NeedfulThings/hyperionconfigs/UDP-ESP8266/assets/top_v1.1.png

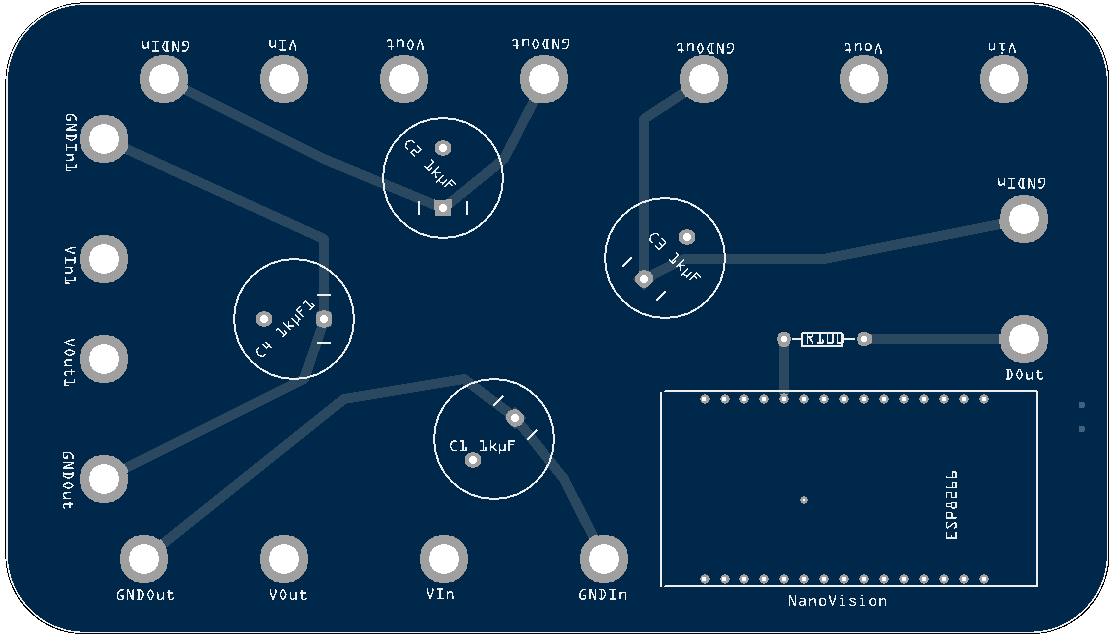
UDP-ESP8266/assets/top_v1.1.png
