NeedfulThings/hyperionconfigs/USB-UDP-Universal/layout/assets/back.png

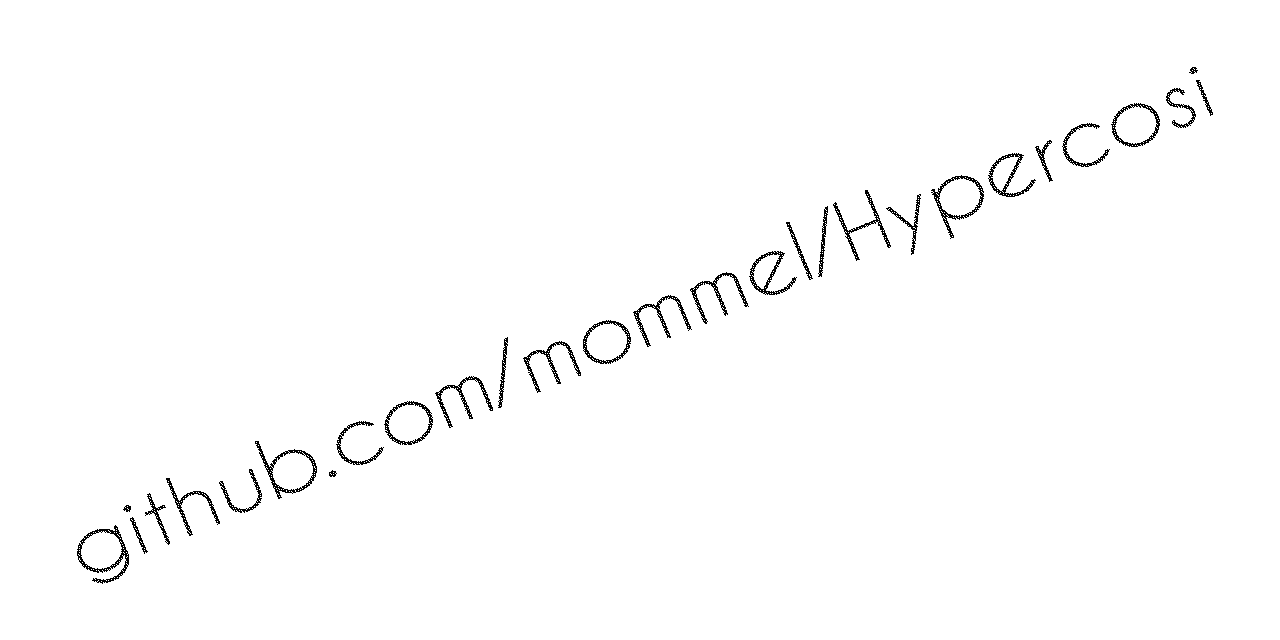
USB-UDP-Universal/layout/assets/back.png
