NeedfulThings/hyperionconfigs/USB-UDP-Universal/layout/assets/hw.png

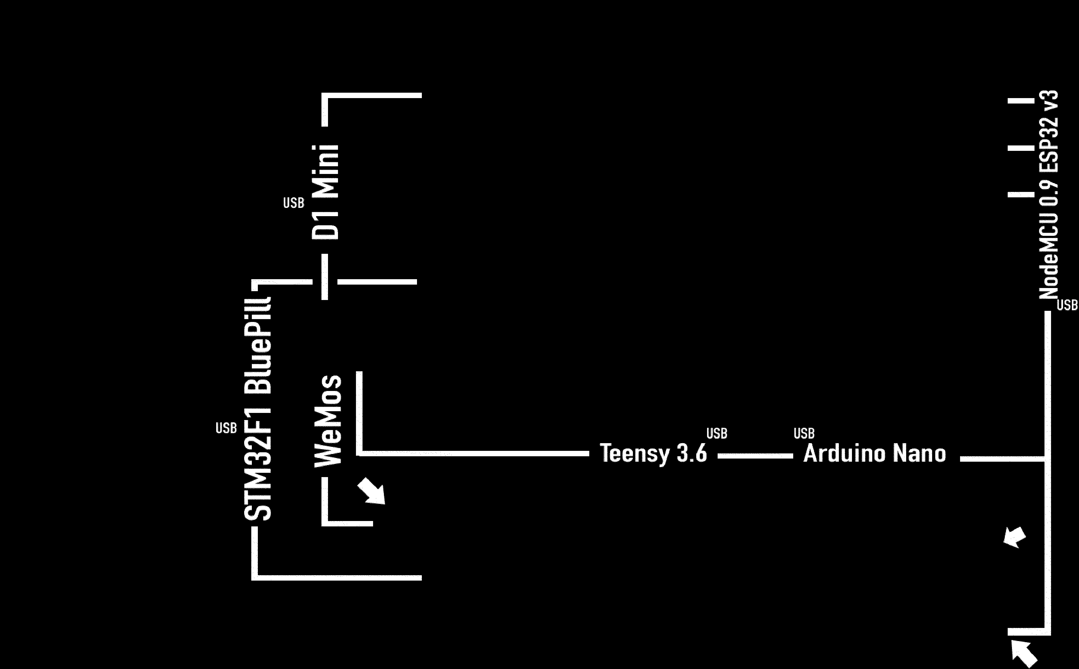
USB-UDP-Universal/layout/assets/hw.png
