NeedfulThings/hyperionconfigs/USB-UDP-Universal/layout/assets/hypercosi_i.png

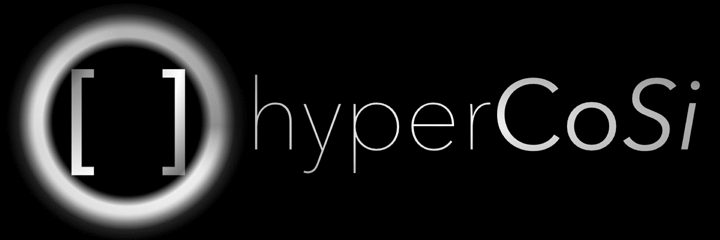
USB-UDP-Universal/layout/assets/hypercosi_i.png
