NeedfulThings/hyperionconfigs/USB-UDP-Universal/layout/assets/plus-i.png

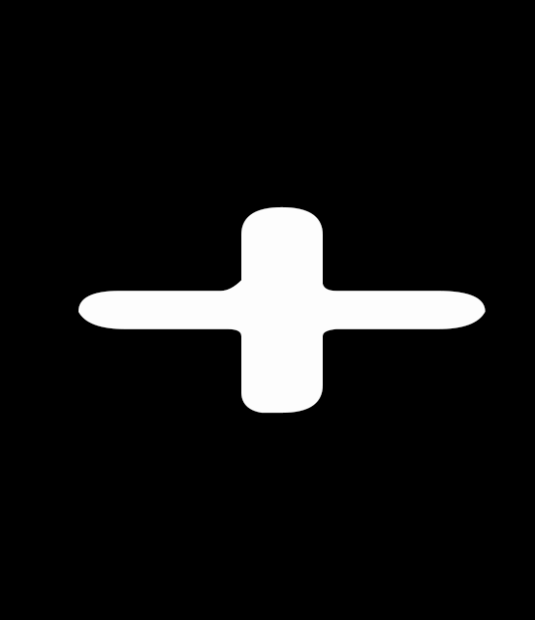
USB-UDP-Universal/layout/assets/plus-i.png
